domhardt/Cellar-Fan-Control/mechanics/WeMos D1 Mini Case/WeMos_Case_5229342/images/01.Base.png

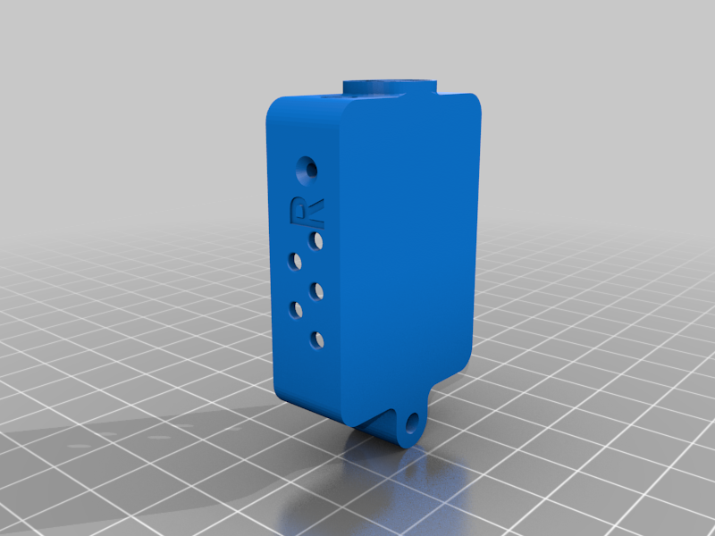
mechanics/WeMos D1 Mini Case/WeMos_Case_5229342/images/01.Base.png
