domhardt/Cellar-Fan-Control/firmware/src/sensor/sensor_BME280.h

#pragma once

// for sensors
#define BME280_POWER_PIN 15

#define BME280_ADDRESS_INSIDE 0x76
#define BME280_ADDRESS_OUTSIDE 0x77

extern unsigned long measureInterval;
extern unsigned long measurementTimestamp;

extern int dewPointThreshold;
extern int minInsideTemperatureCutoff;
extern int minOutsideTemperatureCutoff;

extern float humidityInside;
extern float temperatureInside;
extern float dewPointInside;
extern float dewPointInsideLastSwicthingTime;

extern float humidityOutside;
extern float temperatureOutside;
extern float dewPointOutside;

void initSensors();
void readSensors();
float calcDewPoint(float humidity, float temperature);
void calcDewPoints();
